BmdOnline/EnergyMonitor/hardware/fritzing/Energy Monitor_bb.png

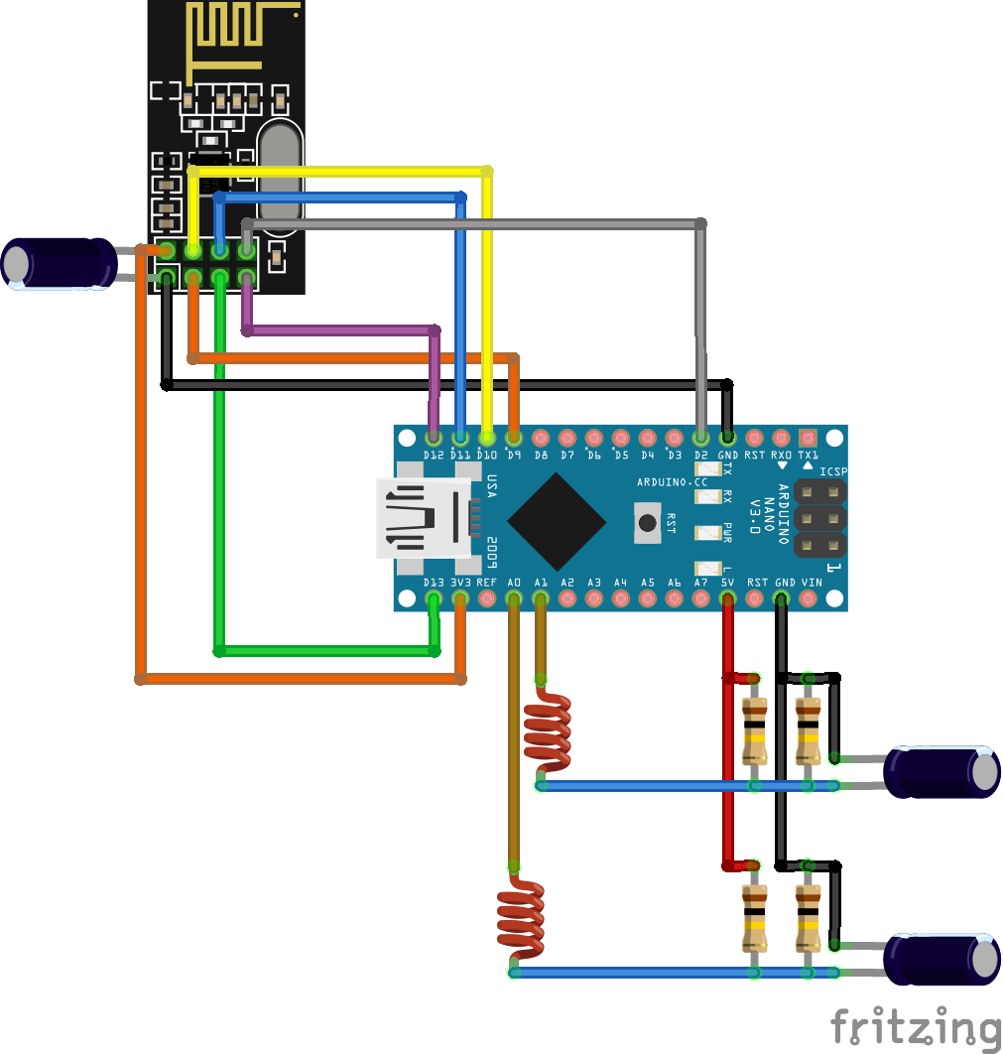
hardware/fritzing/Energy Monitor_bb.png
