BmdOnline/EnergyMonitor/hardware/fritzing/Energy Monitor_sch.png

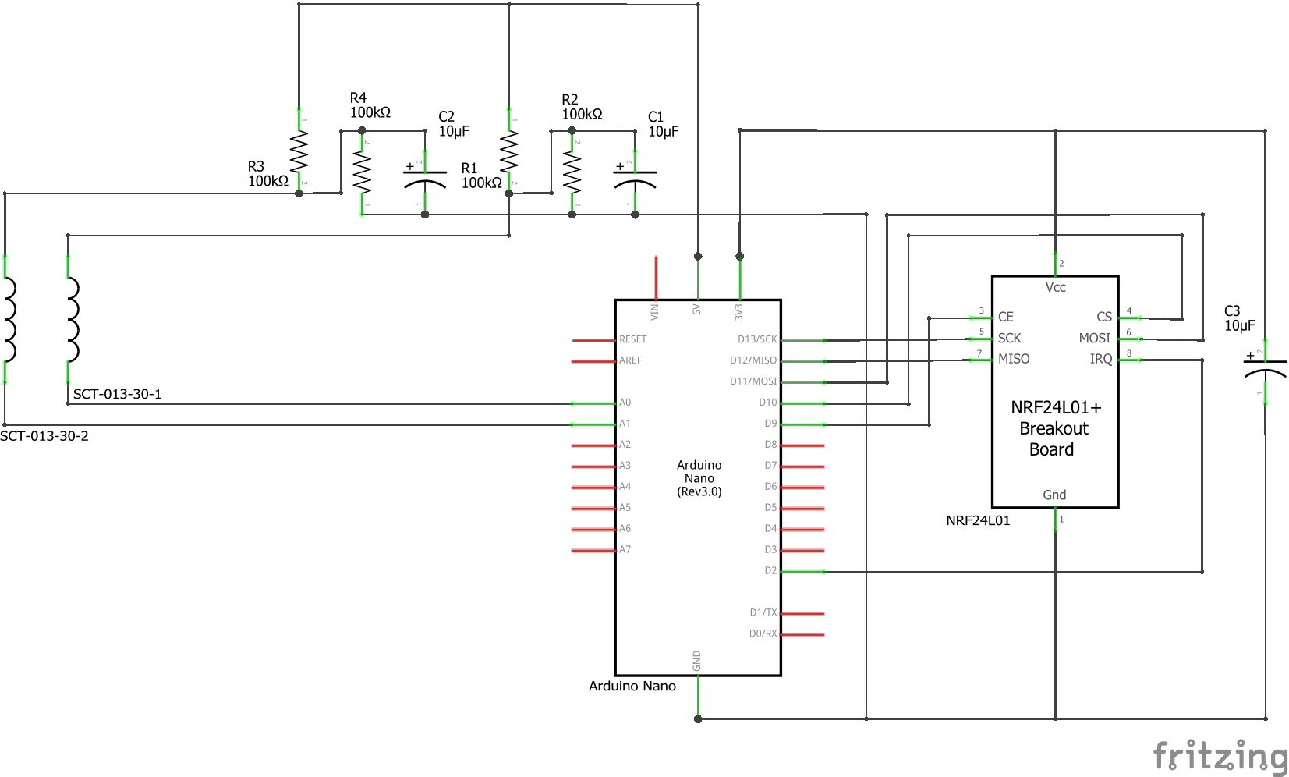
hardware/fritzing/Energy Monitor_sch.png
