BmdOnline/EnergyMonitor/hardware/pictures/IMG_20190603_130150_resize.jpg

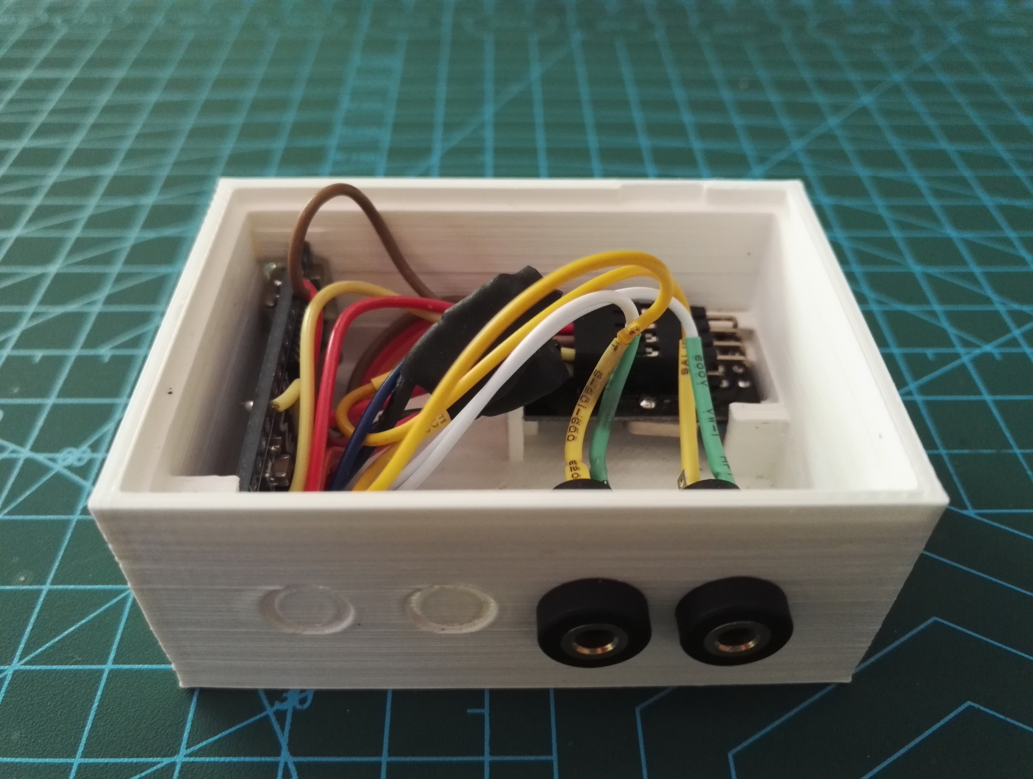
hardware/pictures/IMG_20190603_130150_resize.jpg
