BmdOnline/EnergyMonitor/software/screenshots/Screenshot_2019-06-03 Domoticz_1.png

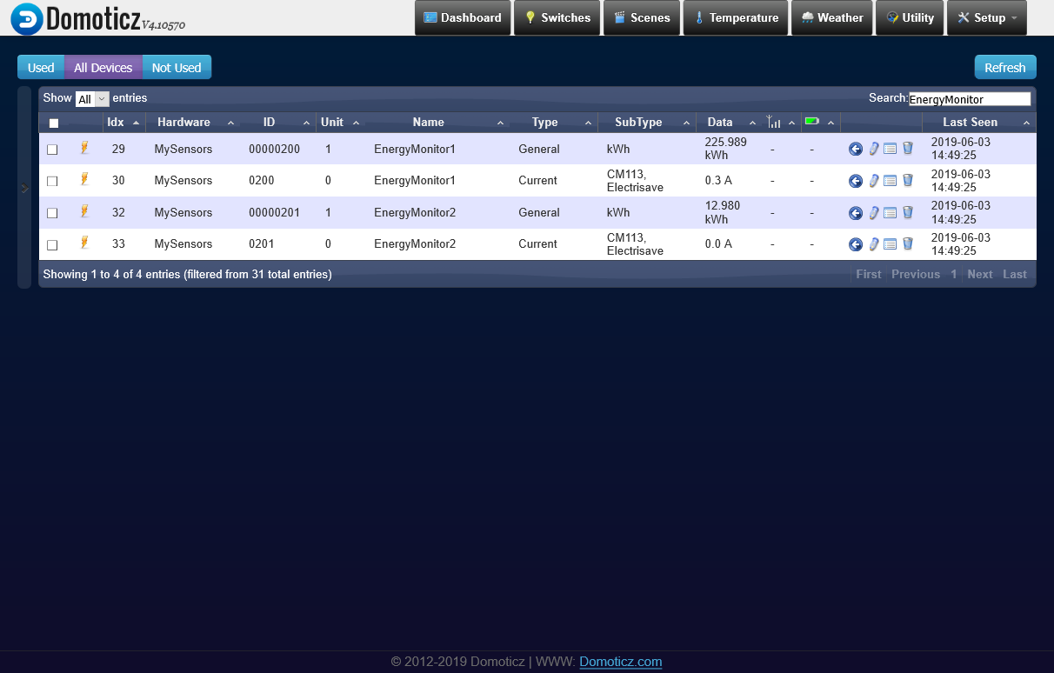
software/screenshots/Screenshot_2019-06-03 Domoticz_1.png
