BmdOnline/EnergyMonitor/software/screenshots/Screenshot_2019-06-03 Domoticz_3.png

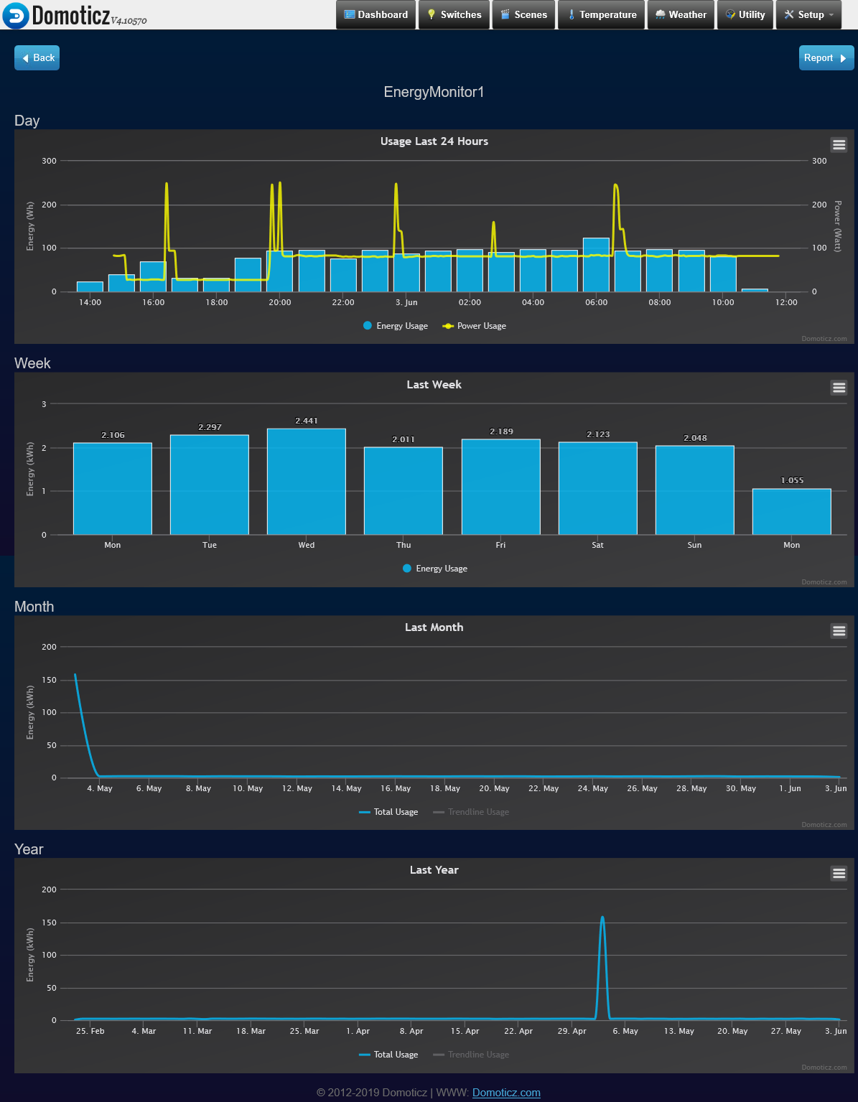
software/screenshots/Screenshot_2019-06-03 Domoticz_3.png
