BmdOnline/EnergyMonitor/software/screenshots/Screenshot_2019-06-03 Domoticz_4.png

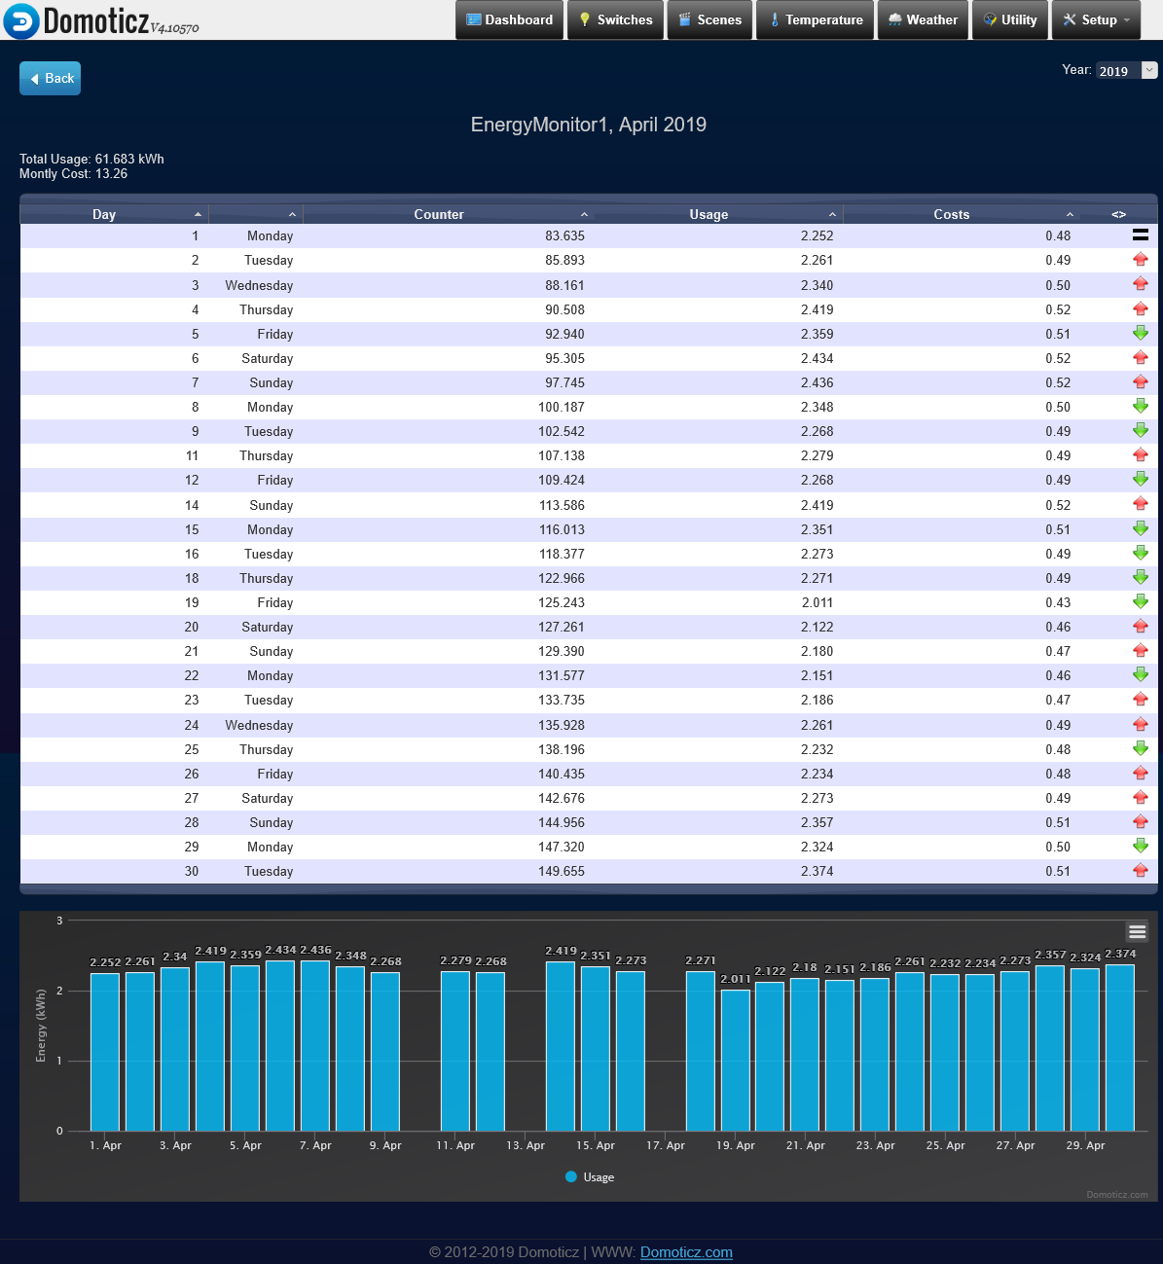
software/screenshots/Screenshot_2019-06-03 Domoticz_4.png
